andrebandarra/tensy/photos/P1160057.JPG

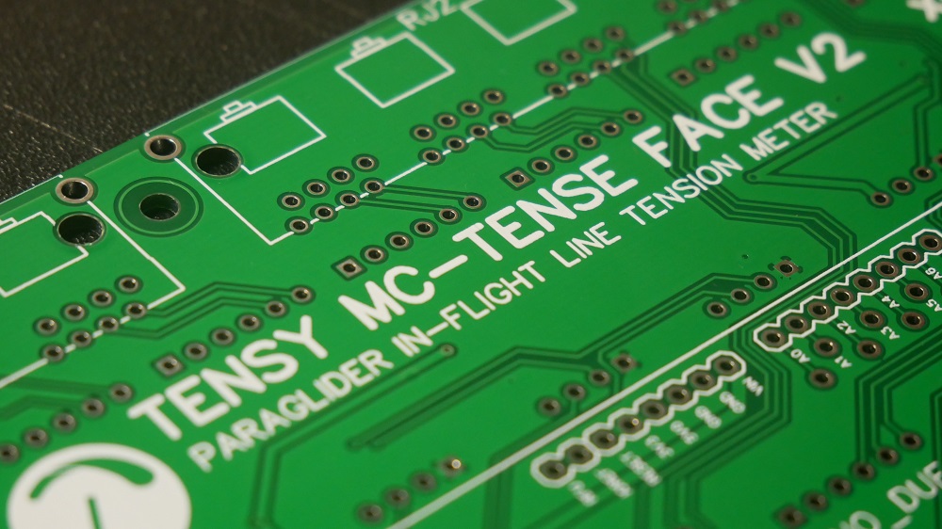
photos/P1160057.JPG
