andrebandarra/tensy/photos/P1160182.JPG

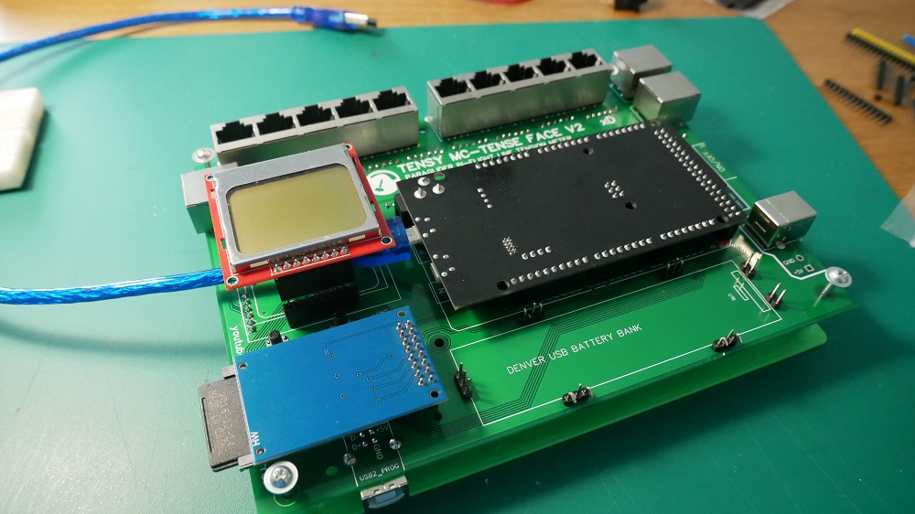
photos/P1160182.JPG
