andrebandarra/tensy/photos/P1160393.JPG

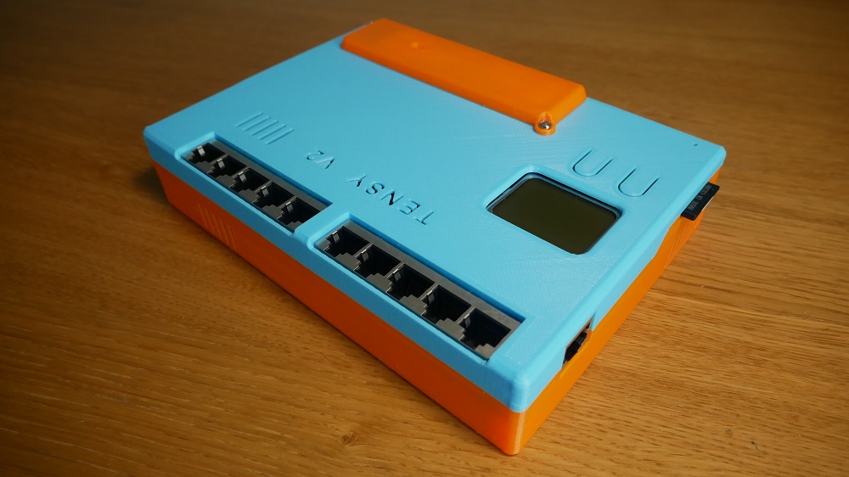
photos/P1160393.JPG
