andrebandarra/tensy/photos/P1160395.JPG

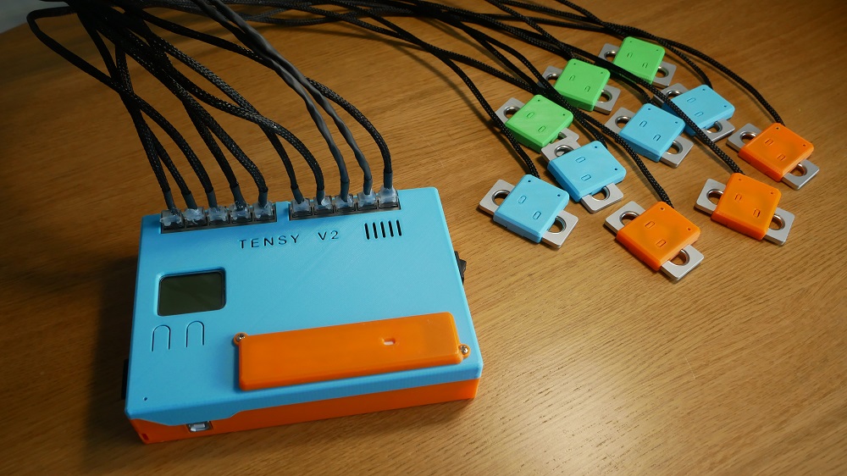
photos/P1160395.JPG
