andrebandarra/tensy/photos/P1160415.JPG

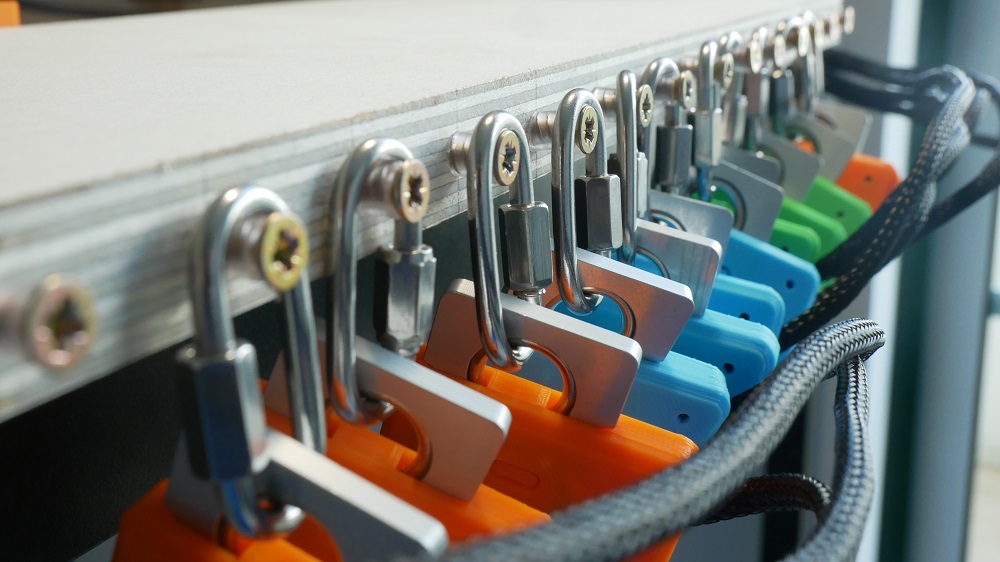
photos/P1160415.JPG
