andrebandarra/tensy/electronics/schematics/holes only Tensy Mc-Tense Face V2 .dxf

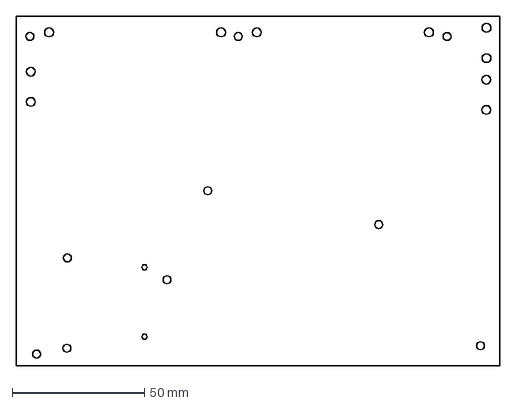
[picture p25: CAD file, 2021-11-13]
electronics/schematics/holes only Tensy Mc-Tense Face V2 .dxf
182.5 x 132.1 mm
