andrebandarra/tensy/cad/riser set/maillon35mm.SLDPRT

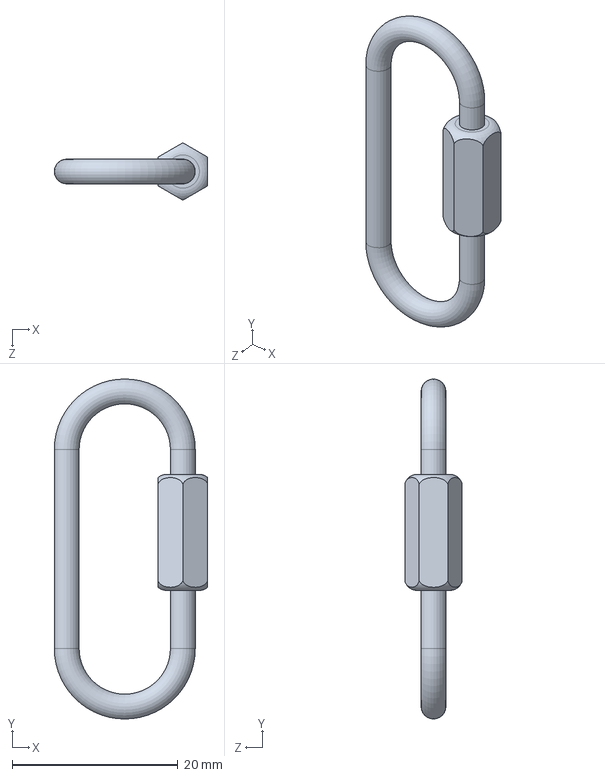
[picture p26: CAD file, 2021-11-13]
cad/riser set/maillon35mm.SLDPRT
18.5 x 41.0 x 6.93 mm
