andrebandarra/tensy/cad/Tensy V2/easy eda original cad/Tensy Mc-Tense Face V2.dxf

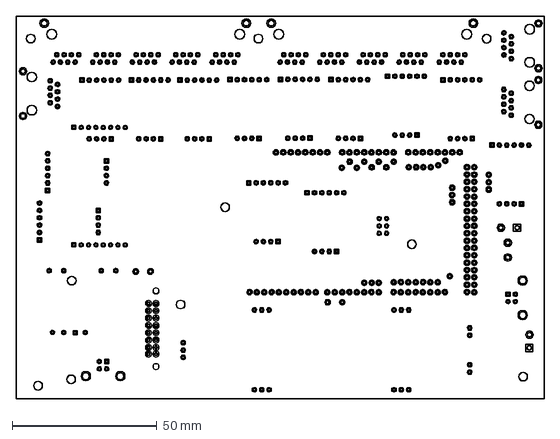
[picture p27: CAD file, 2021-11-13]
cad/Tensy V2/easy eda original cad/Tensy Mc-Tense Face V2.dxf
182.5 x 132.1 mm
