andrebandarra/tensy/cad/Tensy V2/enclosure/sdspacer.SLDPRT

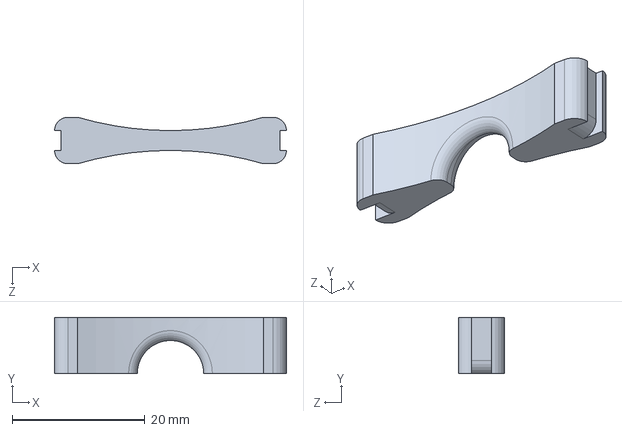
[picture p28: CAD file, 2021-11-13]
cad/Tensy V2/enclosure/sdspacer.SLDPRT
35.0 x 8.50 x 7.00 mm
