andrebandarra/tensy/cad/Tensy V2/load cells/shell2.SLDPRT

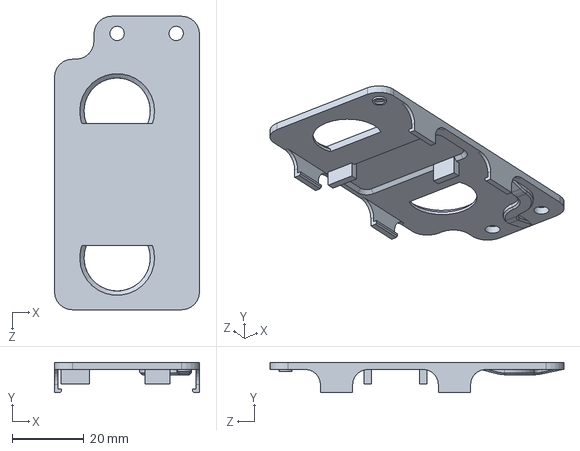
[picture p29: CAD file, 2021-11-13]
cad/Tensy V2/load cells/shell2.SLDPRT
40.5 x 8.50 x 82.0 mm
