andrebandarra/tensy/cad/riser set/A line.SLDPRT

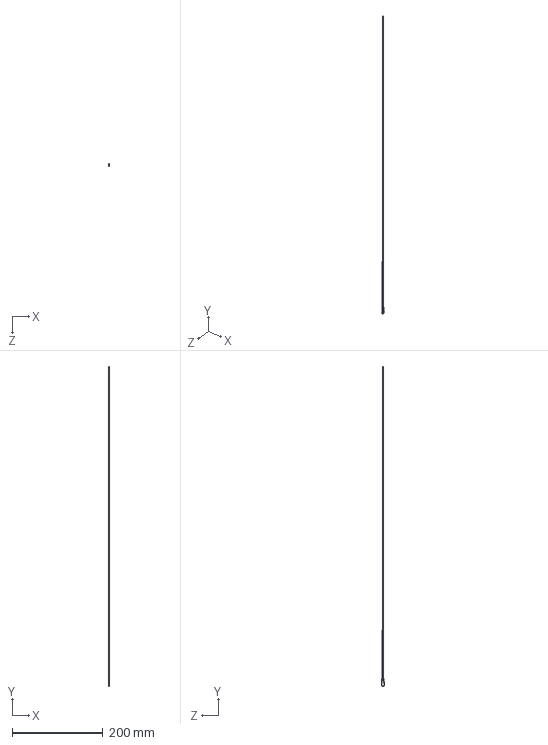
[picture p30: CAD file, 2021-11-13]
cad/riser set/A line.SLDPRT
1.50 x 703.7 x 7.47 mm
