andrebandarra/tensy/cad/Tensy V2/enclosure/top.SLDPRT

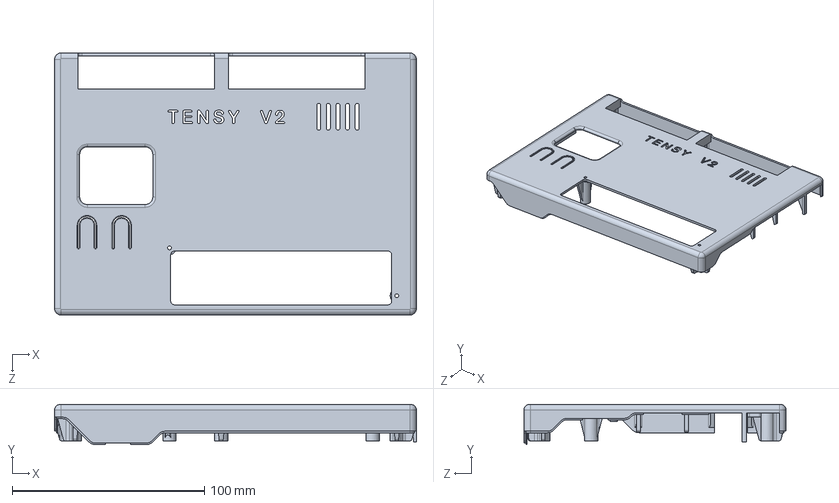
[picture p31: CAD file, 2021-11-13]
cad/Tensy V2/enclosure/top.SLDPRT
188.5 x 21.0 x 136.6 mm
