andrebandarra/tensy/cad/Tensy V2/load cells/shell1.SLDPRT

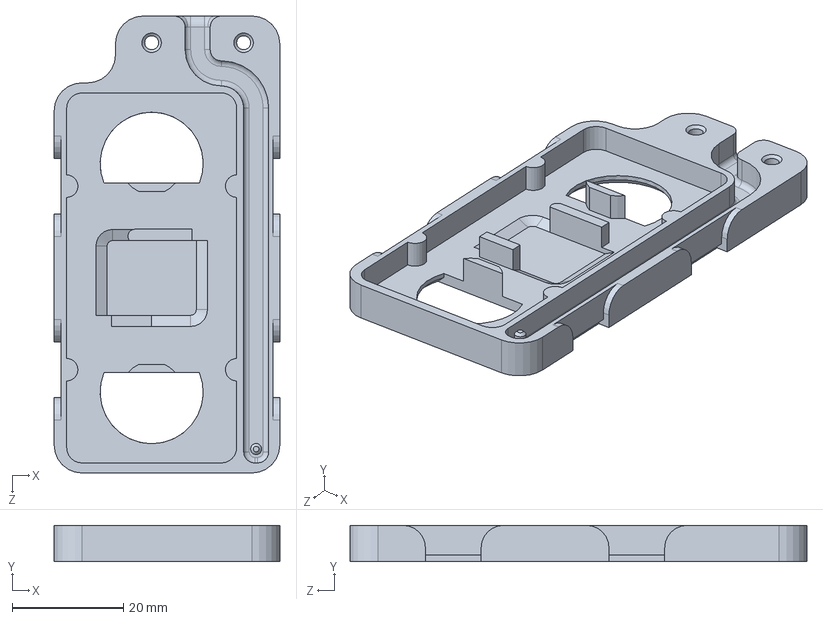
[picture p32: CAD file, 2021-11-13]
cad/Tensy V2/load cells/shell1.SLDPRT
40.5 x 6.50 x 82.0 mm
