andrebandarra/tensy/cad/riser set/risers.SLDPRT

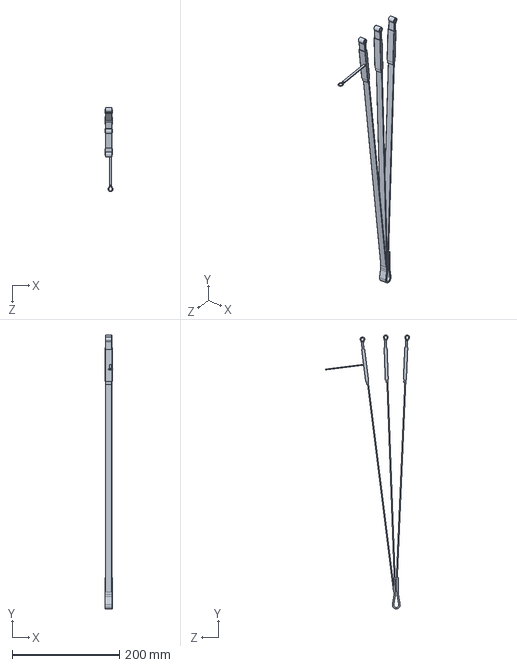
[picture p33: CAD file, 2021-11-13]
cad/riser set/risers.SLDPRT
15.2 x 511.6 x 157.4 mm
