andrebandarra/tensy/cad/Tensy V2/enclosure/bottom.SLDPRT

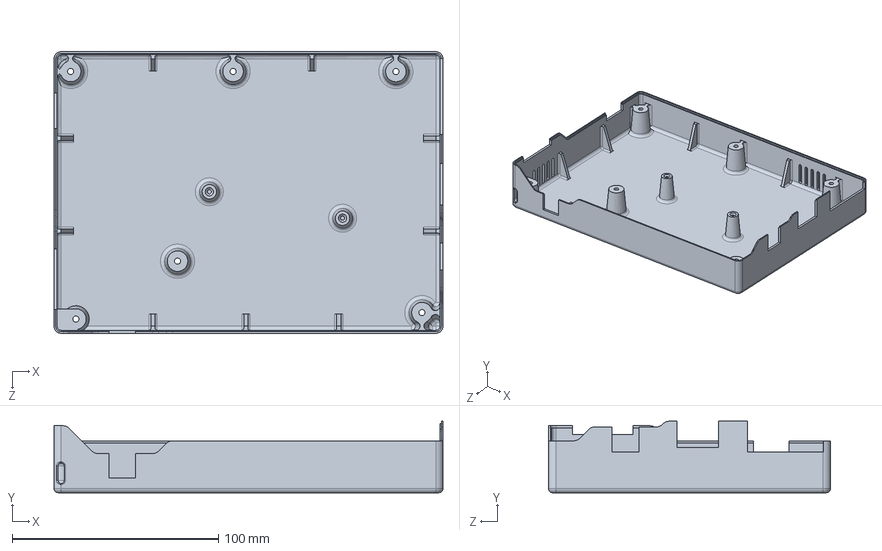
[picture p34: CAD file, 2021-11-13]
cad/Tensy V2/enclosure/bottom.SLDPRT
188.5 x 34.7 x 136.6 mm
