andrebandarra/tensy/cad/riser set/C line.SLDPRT

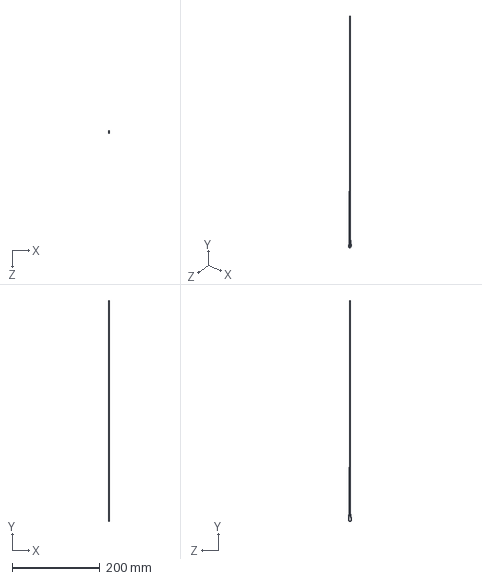
[picture p35: CAD file, 2021-11-13]
cad/riser set/C line.SLDPRT
1.50 x 503.7 x 7.47 mm
