andrebandarra/tensy/cad/Tensy V2/enclosure/bat cover.SLDPRT

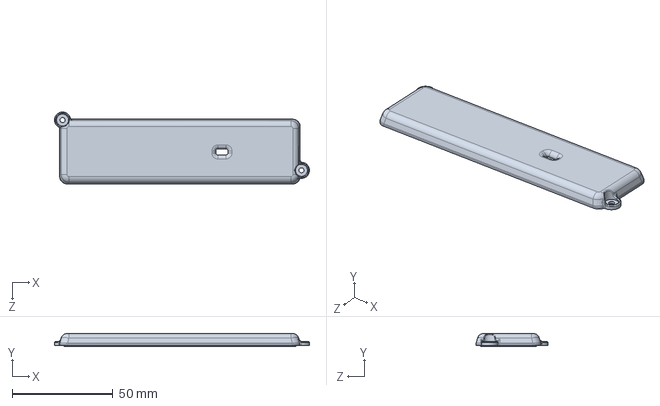
[picture p36: CAD file, 2021-11-13]
cad/Tensy V2/enclosure/bat cover.SLDPRT
126.4 x 6.40 x 35.7 mm
