andrebandarra/tensy/cad/Tensy V2/load cells/shell4.SLDPRT

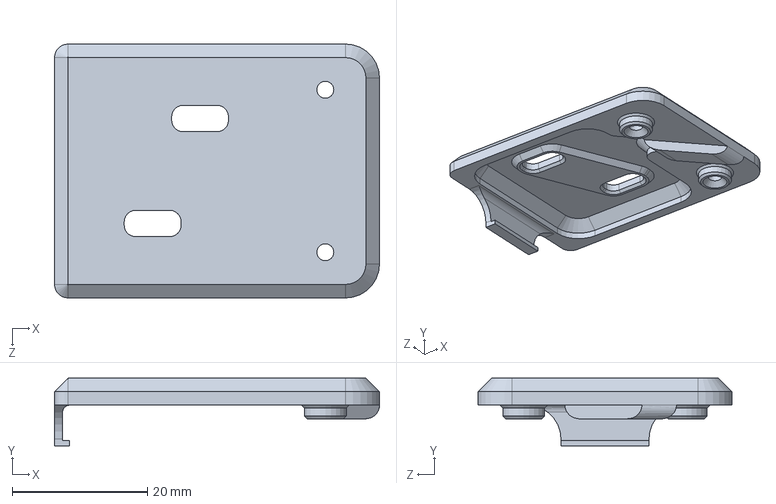
[picture p37: CAD file, 2021-11-13]
cad/Tensy V2/load cells/shell4.SLDPRT
48.0 x 10.0 x 37.5 mm
