andrebandarra/tensy/cad/Tensy V2/load cells/load cell 50kg.SLDPRT

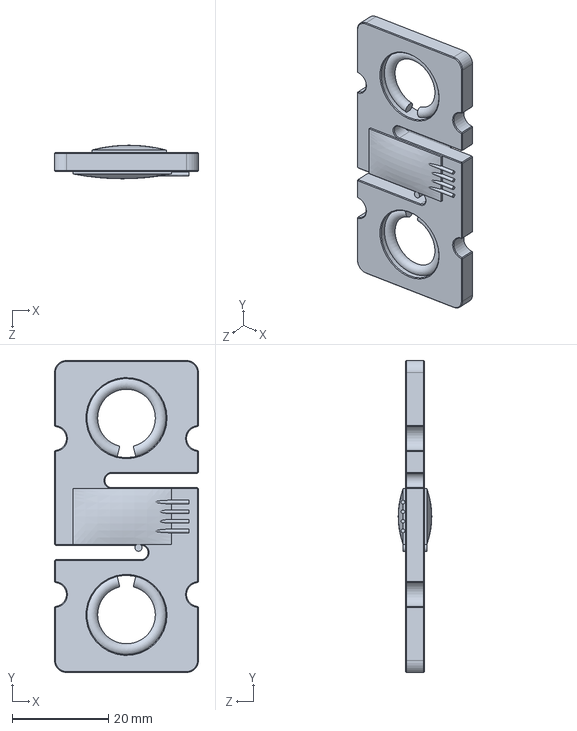
[picture p38: CAD file, 2021-11-13]
cad/Tensy V2/load cells/load cell 50kg.SLDPRT
30.0 x 65.0 x 7.00 mm
