andrebandarra/tensy/cad/riser set/maillon40mm.SLDPRT

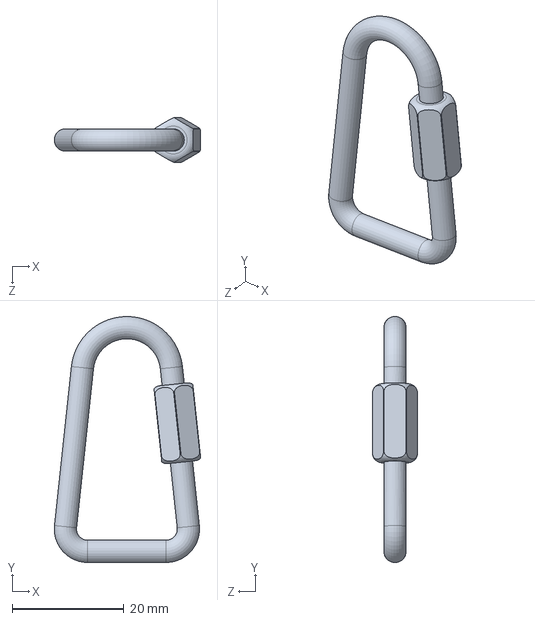
[picture p39: CAD file, 2021-11-13]
cad/riser set/maillon40mm.SLDPRT
26.2 x 44.0 x 8.00 mm
